Eason-Jin/Unojoy-Simulator-Rig/CAD/Indicator/STL Files/Rod.stl

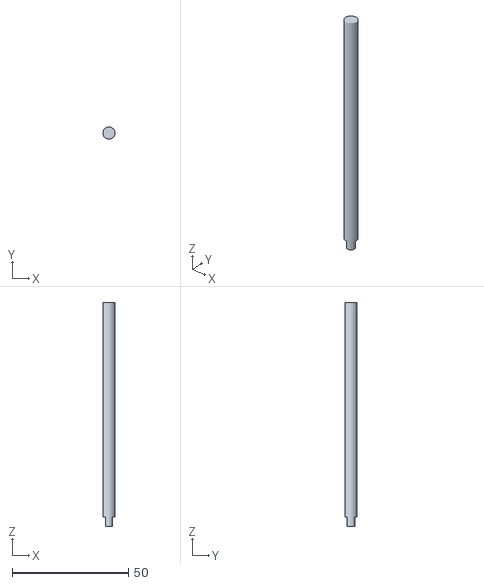
[picture p42: CAD file, 2025-04-13]
CAD/Indicator/STL Files/Rod.stl
5.26 x 5.28 x 96.2
