Eason-Jin/Unojoy-Simulator-Rig/CAD/Pedals/STL Files/Pedal Face Short.stl

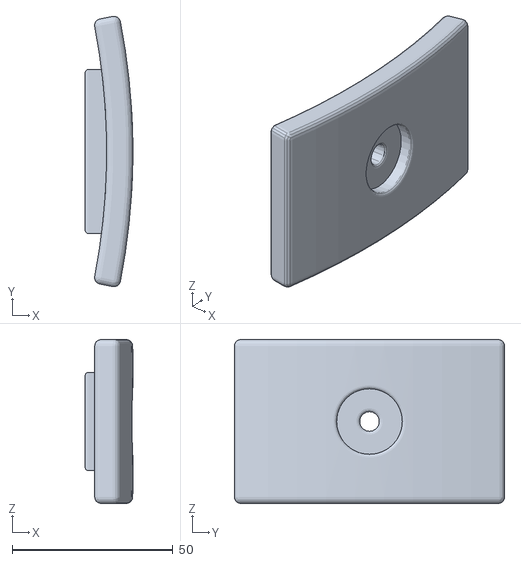
[picture p43: CAD file, 2025-04-13]
CAD/Pedals/STL Files/Pedal Face Short.stl
14.9 x 84.1 x 51.0
