Eason-Jin/Unojoy-Simulator-Rig/CAD/Shift Knob/STL Files/Adapter.stl

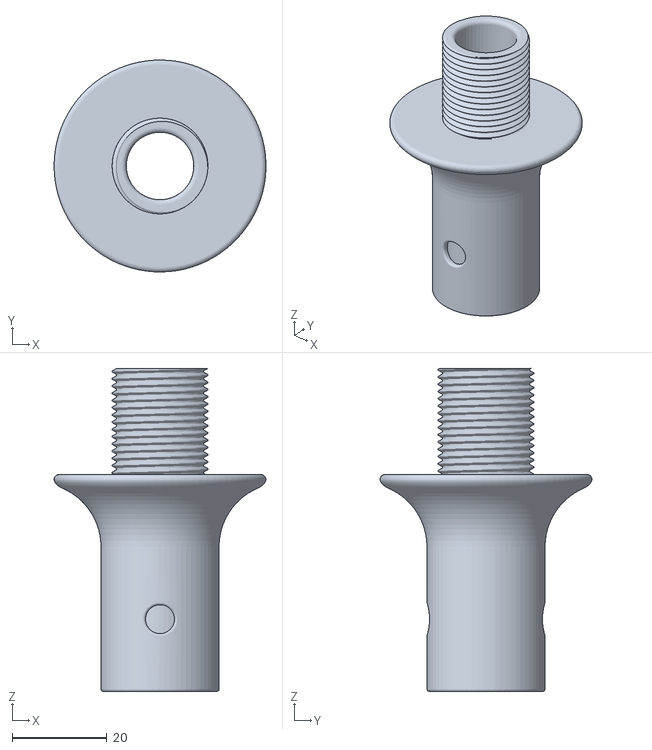
[picture p44: CAD file, 2025-03-16]
CAD/Shift Knob/STL Files/Adapter.stl
44.8 x 44.8 x 68.3
