Eason-Jin/Unojoy-Simulator-Rig/CAD/Shifter/STL Files/Shifter Support.stl

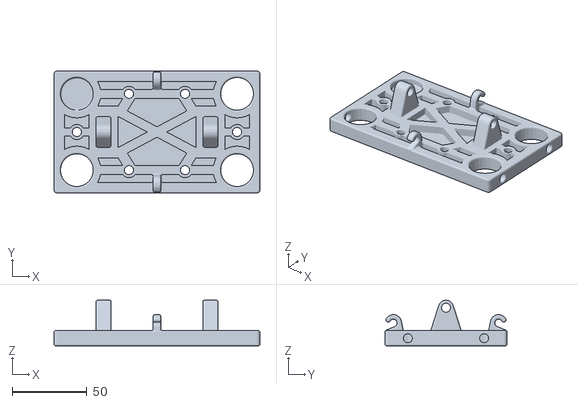
[picture p45: CAD file, 2025-03-16]
CAD/Shifter/STL Files/Shifter Support.stl
137.7 x 81.6 x 30.6
