Eason-Jin/Unojoy-Simulator-Rig/CAD/Steering/STL Files/Steering Mounting Plate 3.stl

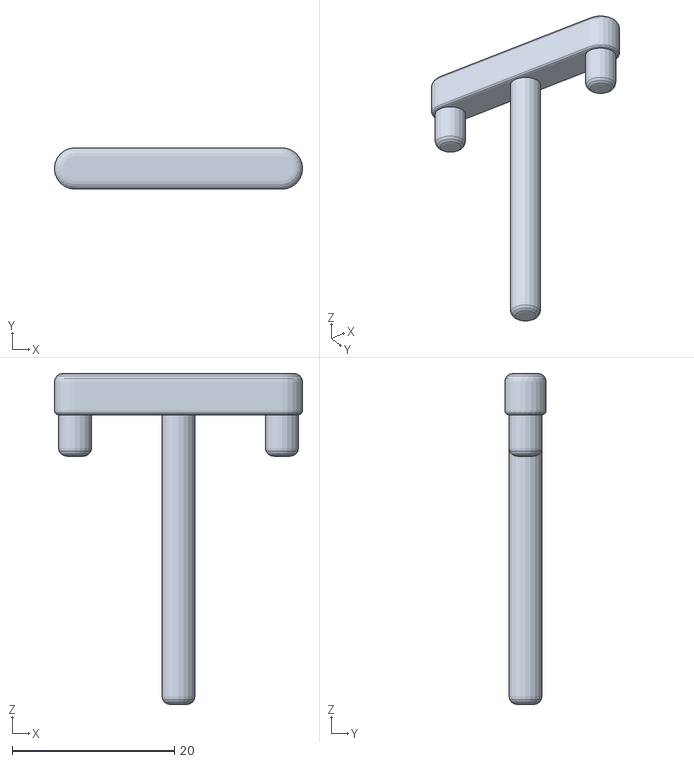
[picture p46: CAD file, 2025-03-16]
CAD/Steering/STL Files/Steering Mounting Plate 3.stl
30.6 x 5.10 x 40.8
