Eason-Jin/Unojoy-Simulator-Rig/CAD/Pedals/STL Files/Pedal Arm Short.stl

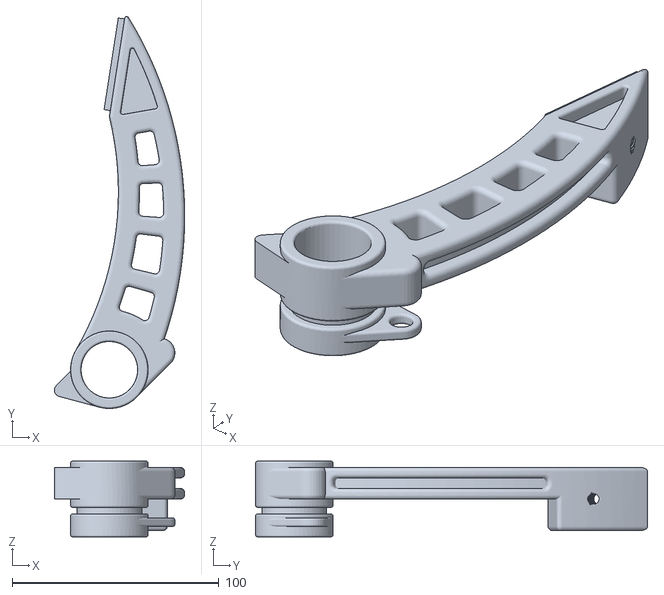
[picture p47: CAD file, 2025-04-13]
CAD/Pedals/STL Files/Pedal Arm Short.stl
63.1 x 189.7 x 36.7
