Eason-Jin/Unojoy-Simulator-Rig/CAD/Shift Knob/STL Files/Joystick.stl

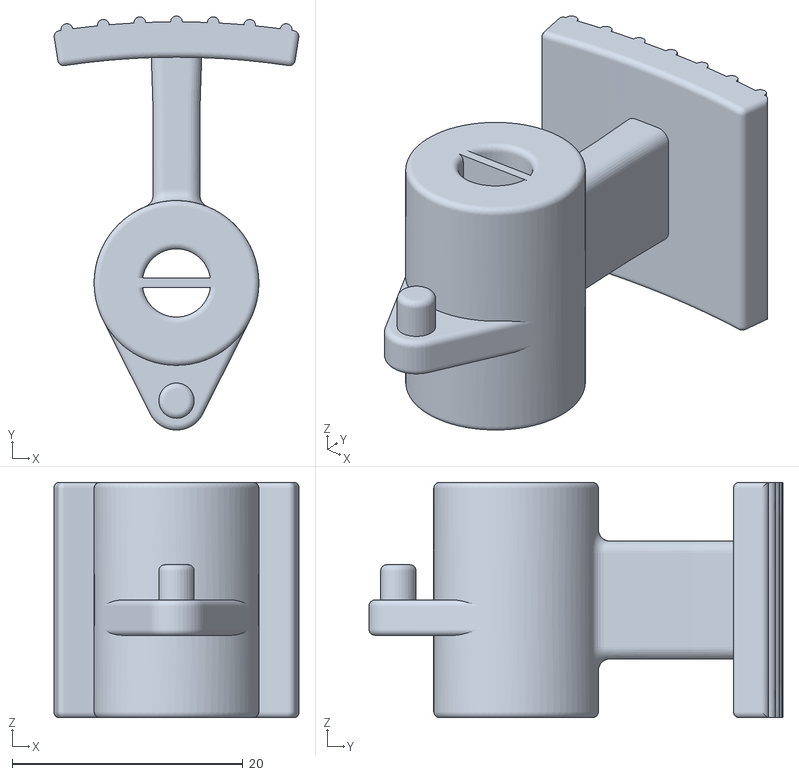
[picture p48: CAD file, 2025-03-16]
CAD/Shift Knob/STL Files/Joystick.stl
21.2 x 35.9 x 20.4
