Eason-Jin/Unojoy-Simulator-Rig/CAD/Steering/STL Files/Encoder Gear.stl

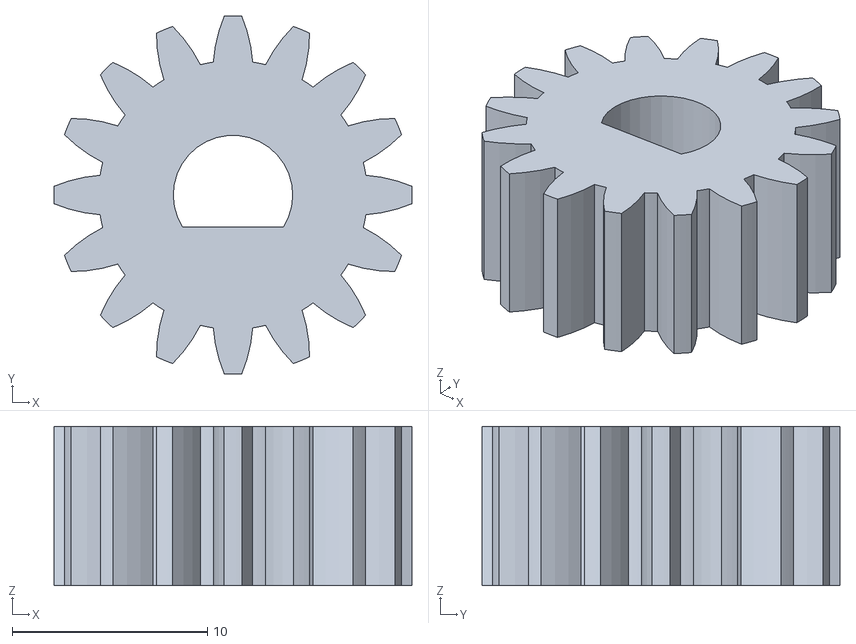
[picture p49: CAD file, 2025-03-16]
CAD/Steering/STL Files/Encoder Gear.stl
18.3 x 18.3 x 8.16
