Eason-Jin/Unojoy-Simulator-Rig/CAD/Pedals/STL Files/Pedal Support R.stl

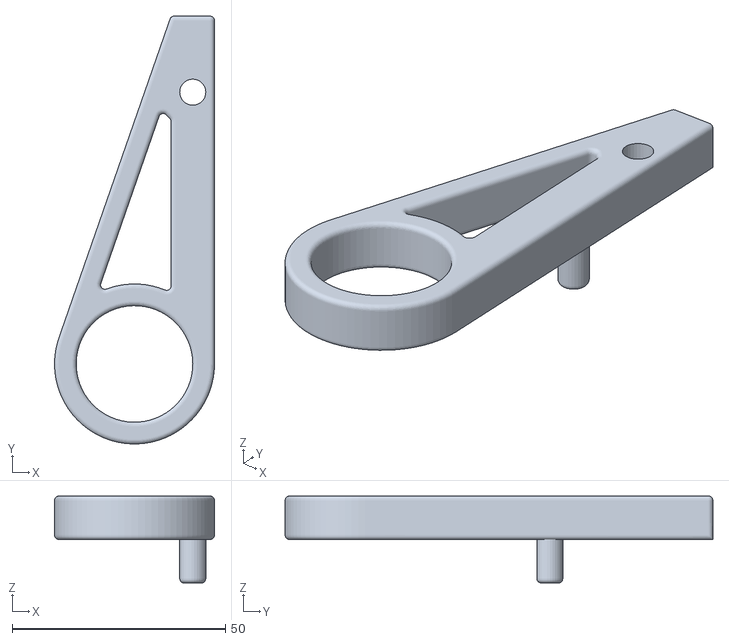
[picture p50: CAD file, 2025-04-13]
CAD/Pedals/STL Files/Pedal Support R.stl
37.5 x 100.4 x 20.4
