Eason-Jin/Unojoy-Simulator-Rig/CAD/Shift Knob/STL Files/Pot Side.stl

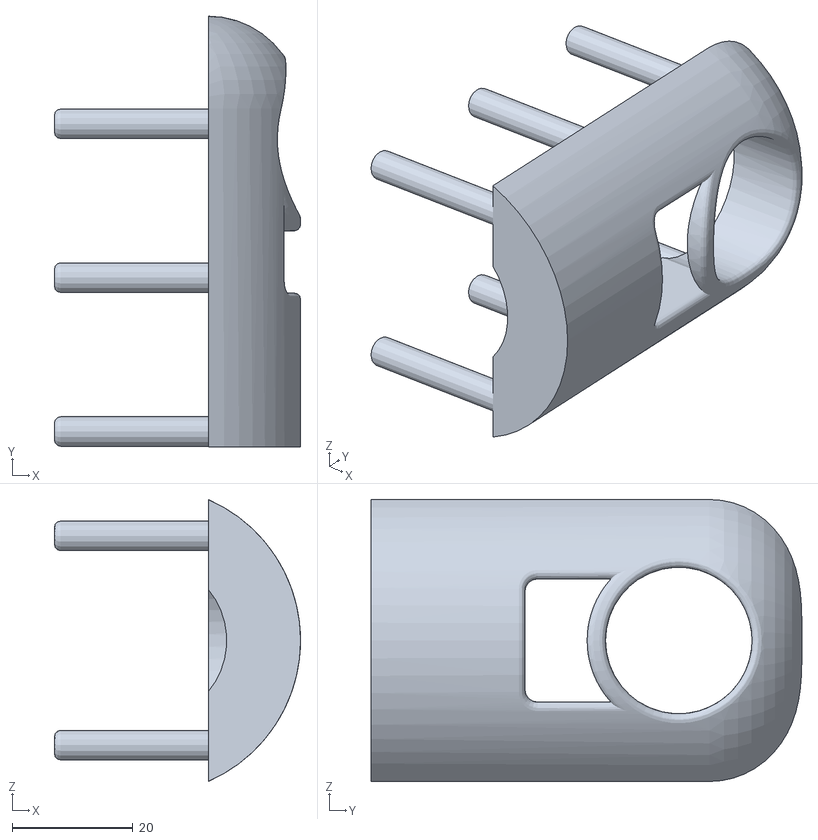
[picture p51: CAD file, 2025-03-16]
CAD/Shift Knob/STL Files/Pot Side.stl
40.8 x 71.4 x 46.7
