Eason-Jin/Unojoy-Simulator-Rig/CAD/Steering/STL Files/Steering Back.stl

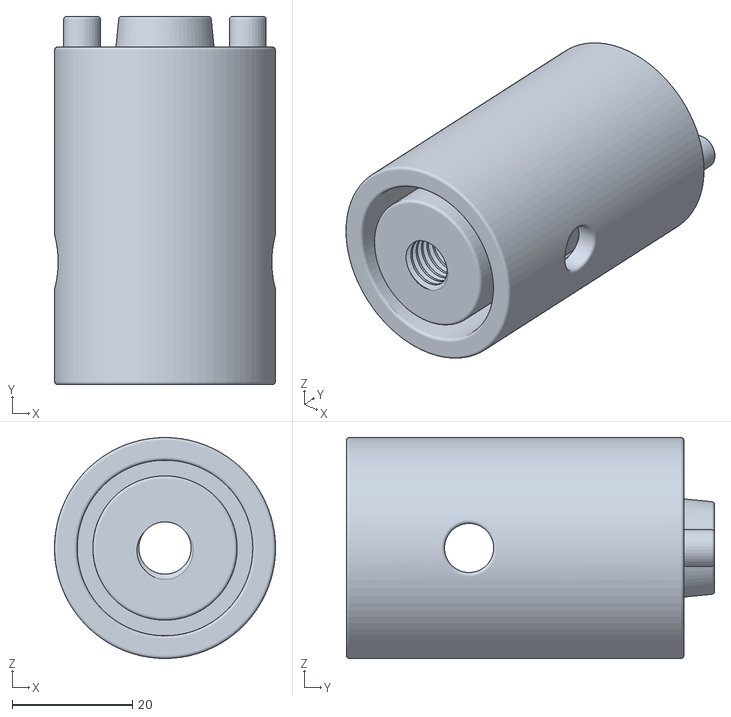
[picture p52: CAD file, 2025-03-16]
CAD/Steering/STL Files/Steering Back.stl
36.7 x 61.2 x 36.7
