Eason-Jin/Unojoy-Simulator-Rig/CAD/Pedals/STL Files/Pedal 1.stl

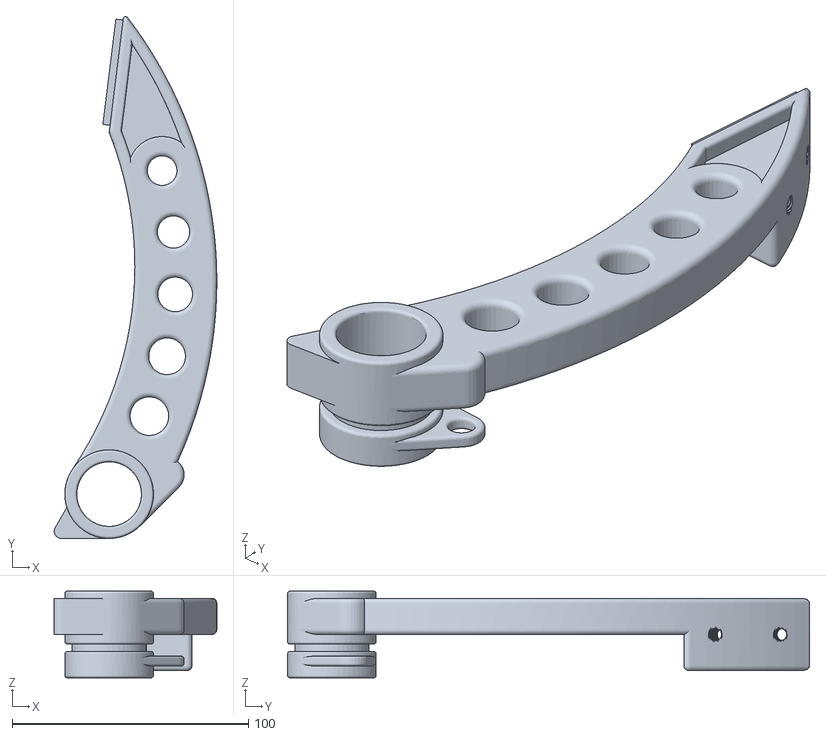
[picture p53: CAD file, 2025-04-13]
CAD/Pedals/STL Files/Pedal 1.stl
68.8 x 220.8 x 36.7
