Eason-Jin/Unojoy-Simulator-Rig/CAD/Shift Knob/STL Files/Joystick Extra Hook.stl

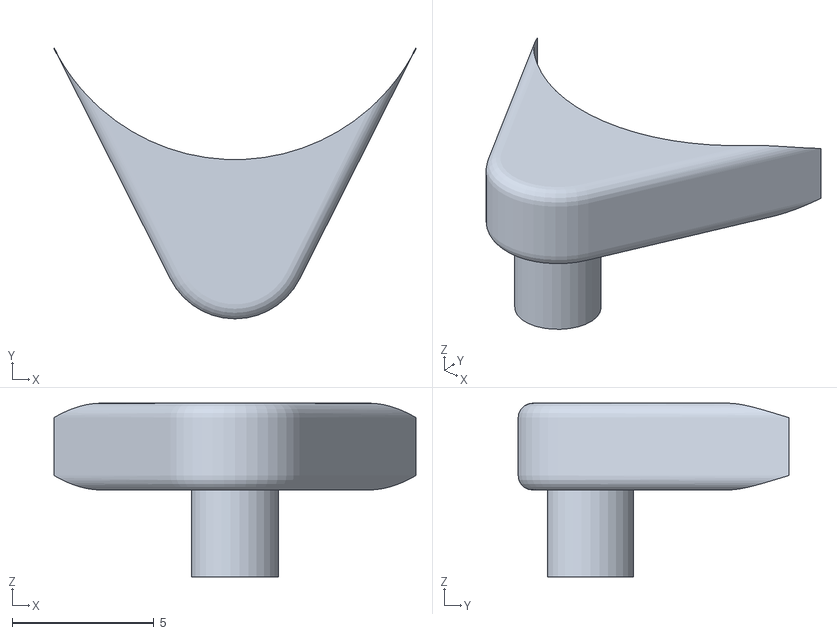
[picture p54: CAD file, 2025-03-16]
CAD/Shift Knob/STL Files/Joystick Extra Hook.stl
12.8 x 9.54 x 6.12
