Eason-Jin/Unojoy-Simulator-Rig/CAD/Steering/STL Files/Steering Mounting Plate 1.stl

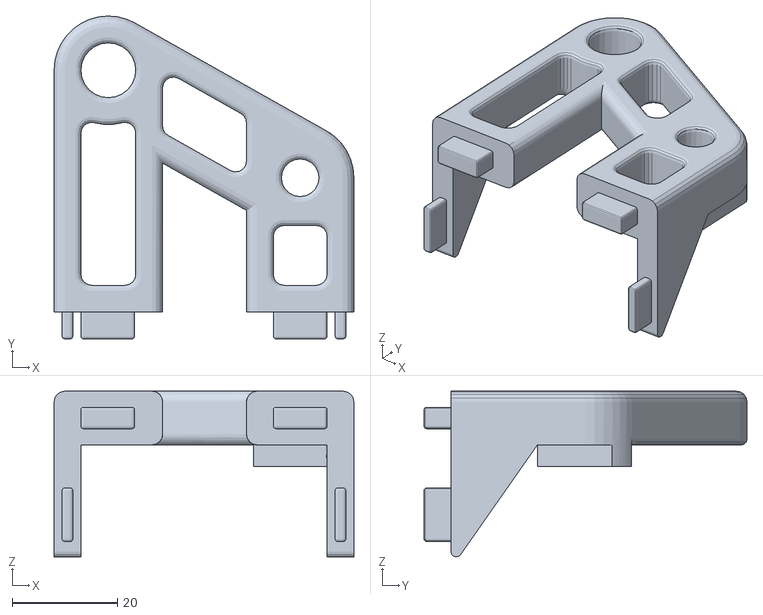
[picture p55: CAD file, 2025-03-16]
CAD/Steering/STL Files/Steering Mounting Plate 1.stl
56.9 x 61.3 x 31.5
