Eason-Jin/Unojoy-Simulator-Rig/CAD/Pedals/STL Files/Pedal 2.stl

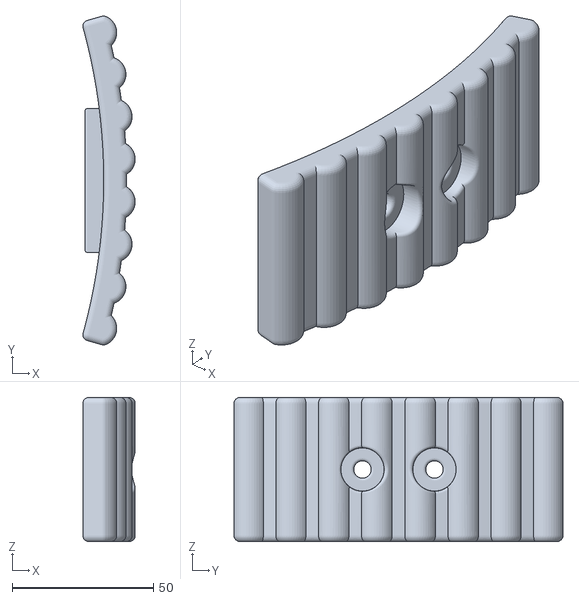
[picture p56: CAD file, 2025-04-13]
CAD/Pedals/STL Files/Pedal 2.stl
18.5 x 116.5 x 51.0
