Eason-Jin/Unojoy-Simulator-Rig/CAD/Steering/STL Files/Axle.stl

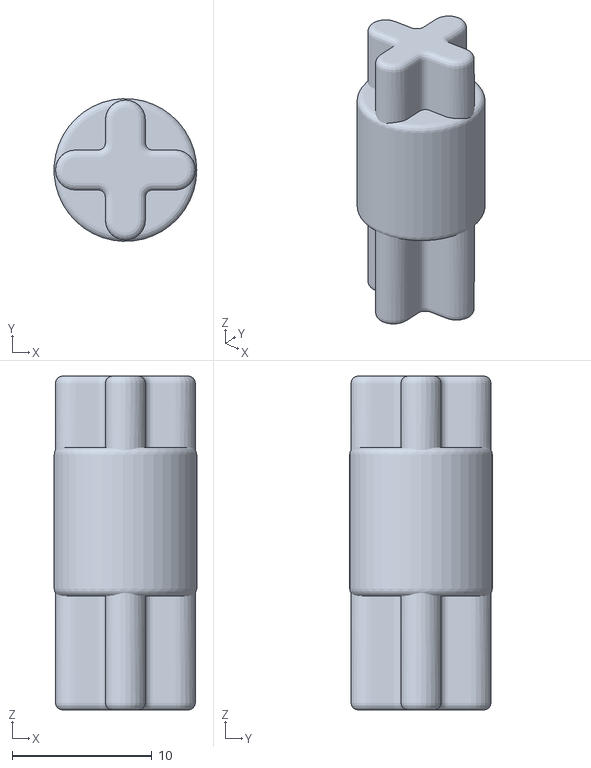
[picture p57: CAD file, 2025-03-16]
CAD/Steering/STL Files/Axle.stl
10.2 x 10.2 x 23.9
