Eason-Jin/Unojoy-Simulator-Rig/CAD/Pedals/STL Files/Pedal Support 1.stl

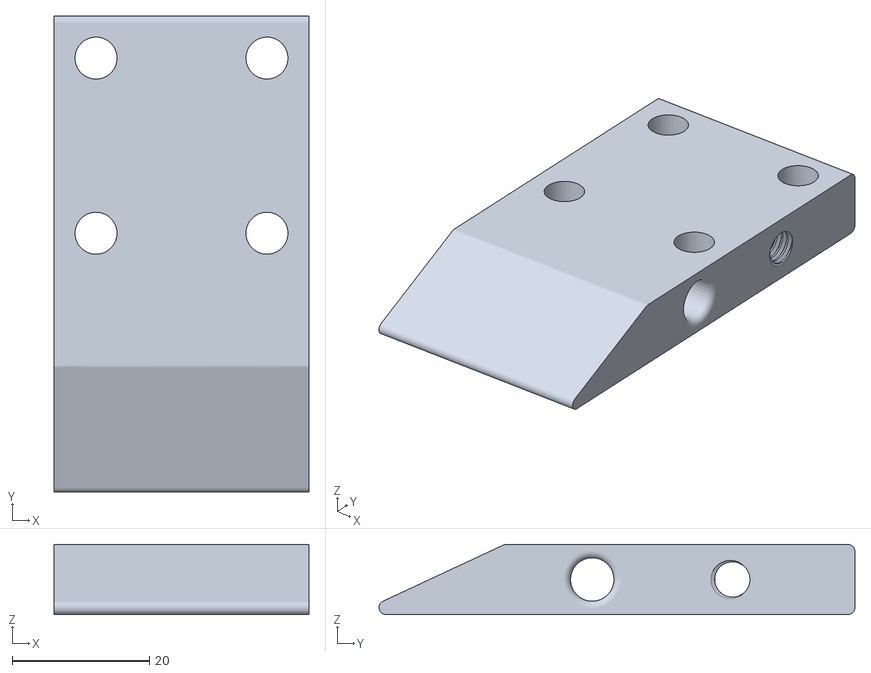
[picture p58: CAD file, 2025-04-13]
CAD/Pedals/STL Files/Pedal Support 1.stl
37.1 x 69.3 x 10.2
