Eason-Jin/Unojoy-Simulator-Rig/CAD/Steering/STL Files/Steering Gear.stl

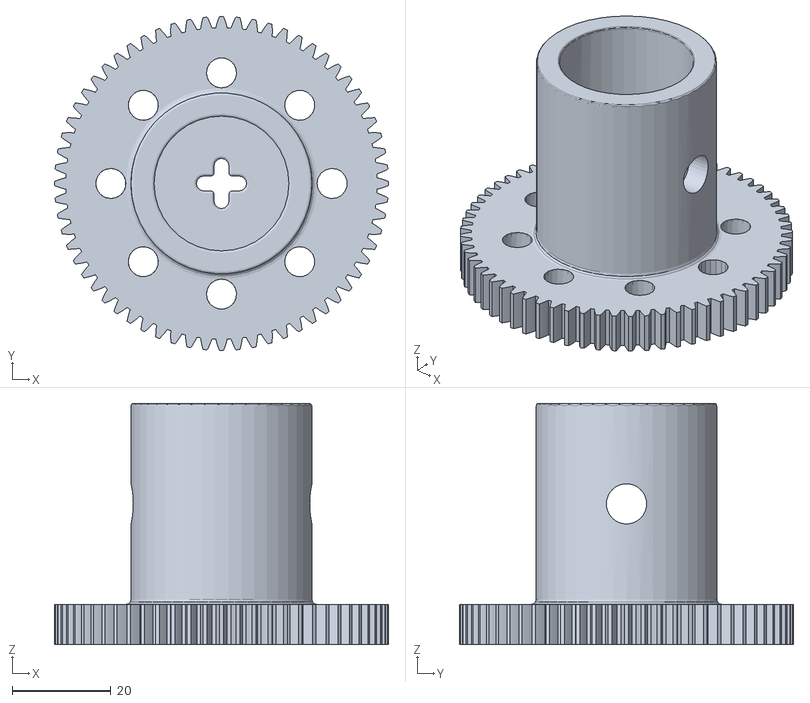
[picture p59: CAD file, 2025-03-16]
CAD/Steering/STL Files/Steering Gear.stl
67.8 x 67.8 x 49.0
