Eason-Jin/Unojoy-Simulator-Rig/CAD/Steering/STL Files/Steering Gear Plate 2.stl

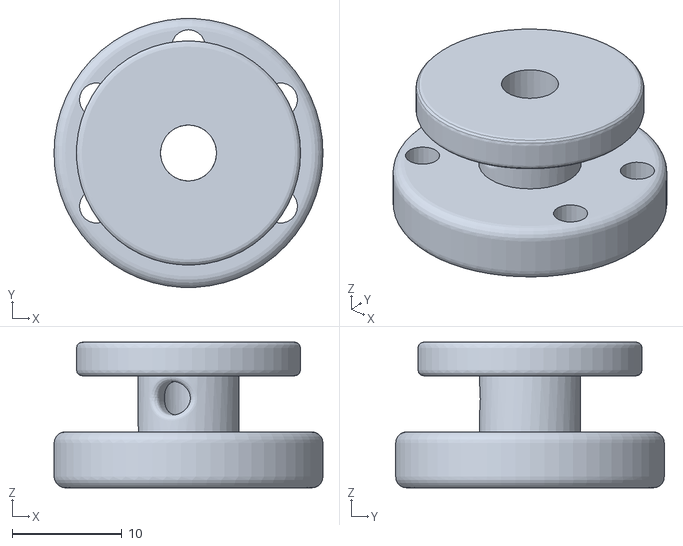
[picture p60: CAD file, 2025-03-16]
CAD/Steering/STL Files/Steering Gear Plate 2.stl
24.5 x 24.4 x 13.3
