Eason-Jin/Unojoy-Simulator-Rig/CAD/Steering/STL Files/Locating Pin.stl

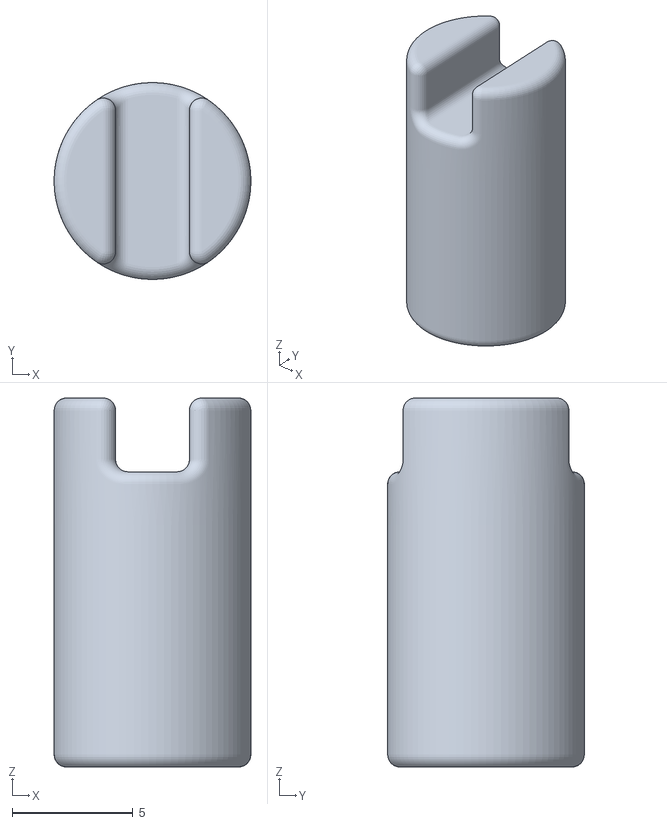
[picture p61: CAD file, 2025-03-16]
CAD/Steering/STL Files/Locating Pin.stl
8.16 x 8.16 x 15.3
