Eason-Jin/Unojoy-Simulator-Rig/CAD/Steering/STL Files/Steering Front.stl

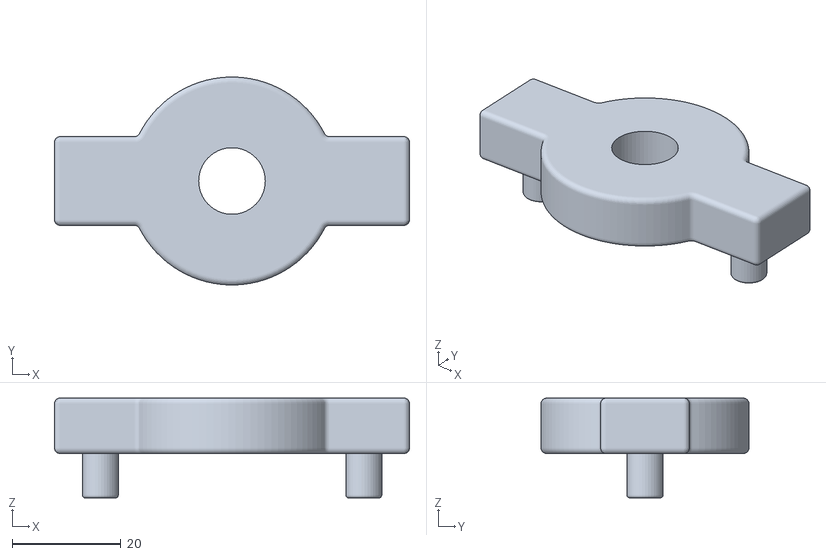
[picture p62: CAD file, 2025-03-16]
CAD/Steering/STL Files/Steering Front.stl
65.3 x 38.2 x 18.4
